Vibrant-Media-Lab/OdysseyNowDaughterCards/OdysseyDaughterCardSpotGenerator/pdf/OdysseyDaughterCardSpotGenerator-B_Cu.pdf

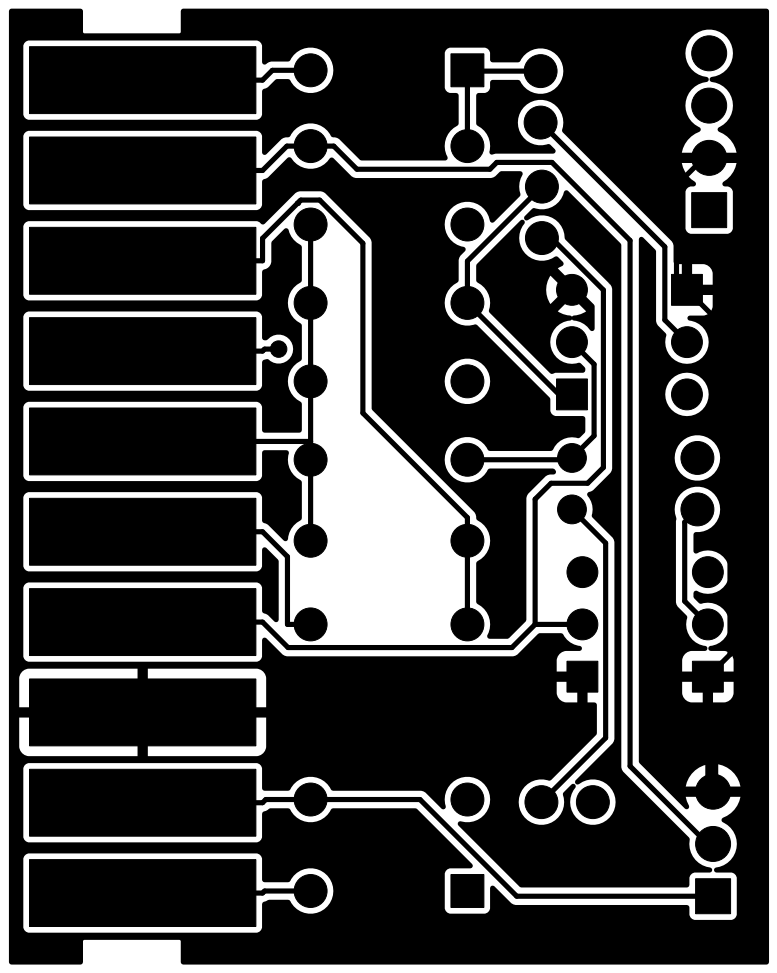
[picture p24: page 1]
