Vibrant-Media-Lab/OdysseyNowDaughterCards/OdysseyDaughterCardSpotGenerator/pdf/OdysseyDaughterCardSpotGenerator-Edge_Cuts.pdf

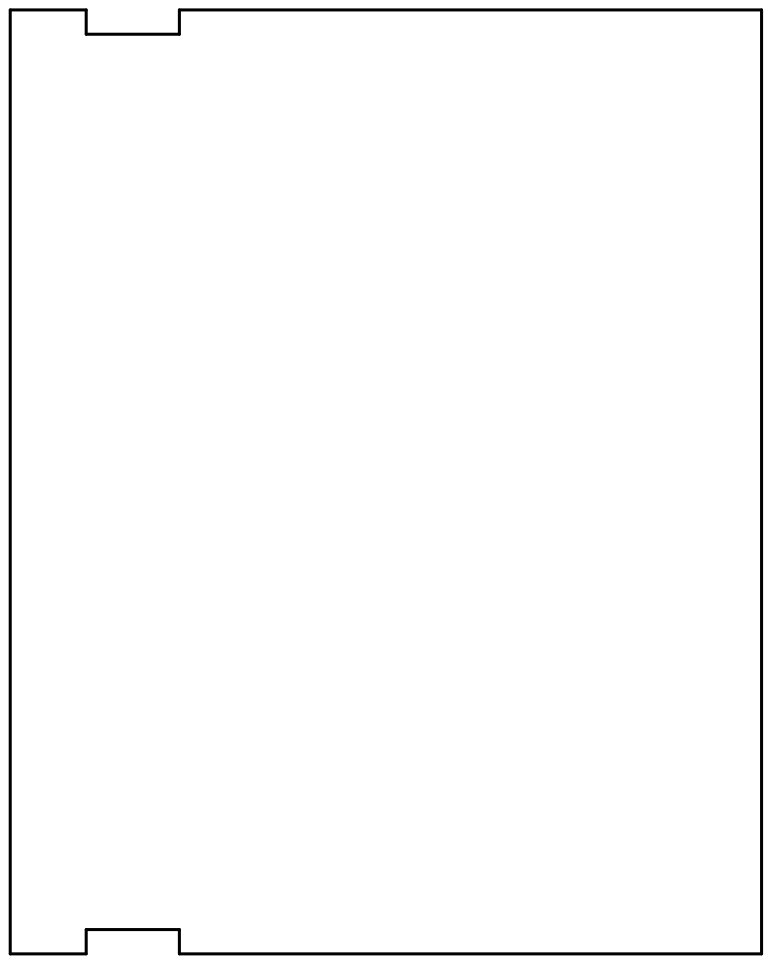
[picture p25: page 1]
