Vibrant-Media-Lab/OdysseyNowDaughterCards/OdysseyDaughterCardSpotGenerator/pdf/OdysseyDaughterCardSpotGenerator-F_Cu.pdf

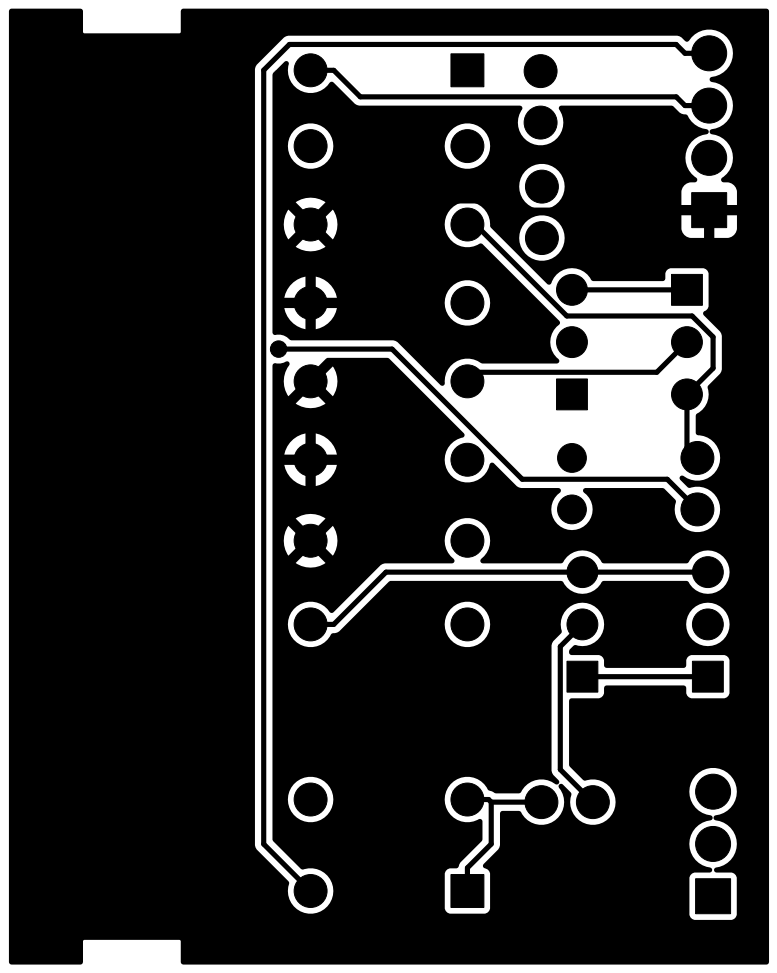
[picture p26: page 1]
