Vibrant-Media-Lab/OdysseyNowDaughterCards/OdysseyDaughterCardSpotGenerator/pdf/OdysseyDaughterCardSpotGenerator-F_Silkscreen.pdf

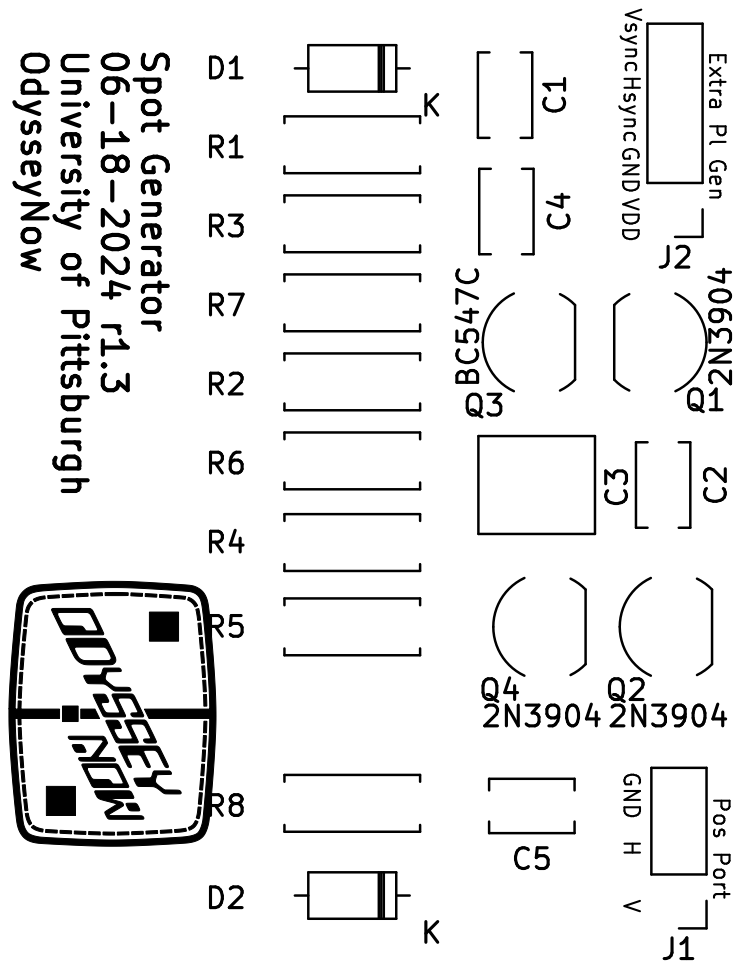
[picture p27: page 1]
