Vibrant-Media-Lab/OdysseyNowDaughterCards/OdysseyDaughterCardSpotGenerator/pdf/OdysseyDaughterCardSpotGenerator.pdf

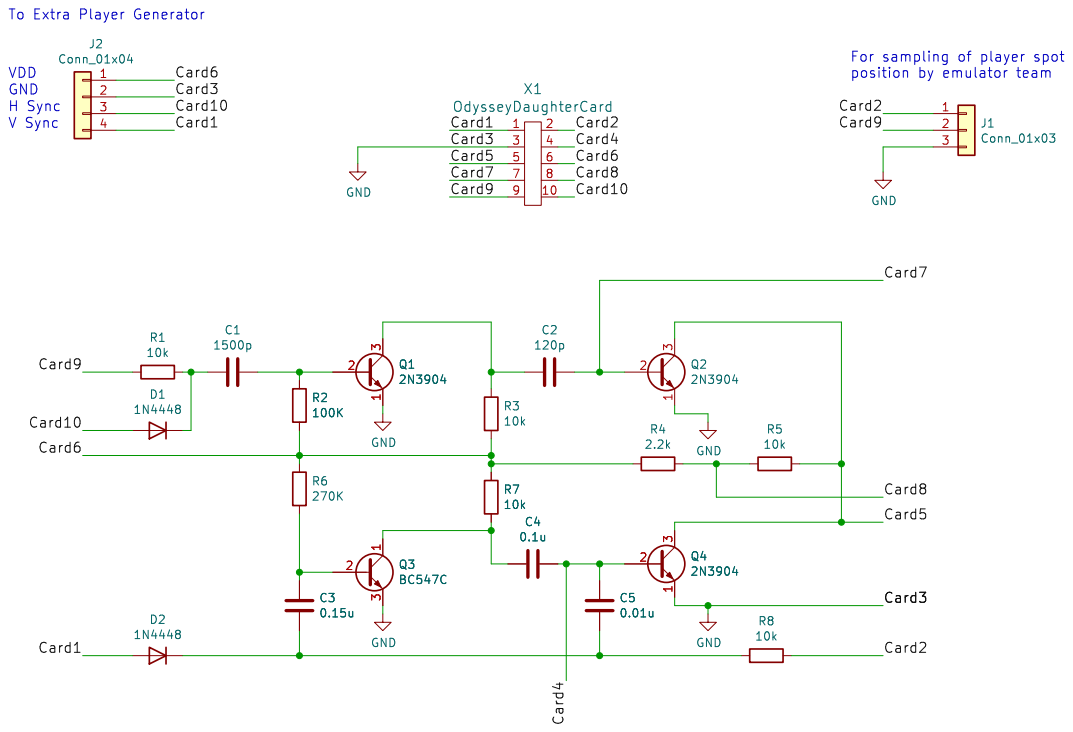
[picture p28: page 1]
