Vibrant-Media-Lab/OdysseyNowDaughterCards/OdysseyDaughterCardHorizSyncGenerator/pdf/OdysseyDaughterCardHorizSyncGenerator-B_Cu.pdf

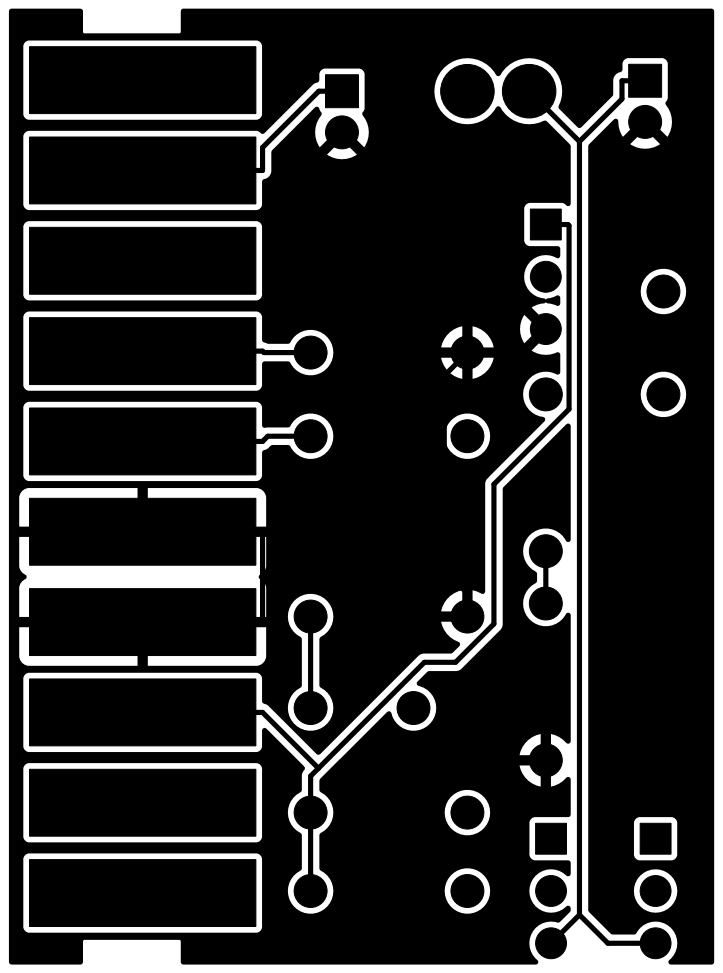
[picture p29: page 1]
