Vibrant-Media-Lab/OdysseyNowDaughterCards/OdysseyDaughterCardHorizSyncGenerator/pdf/OdysseyDaughterCardHorizSyncGenerator-Edge_Cuts.pdf

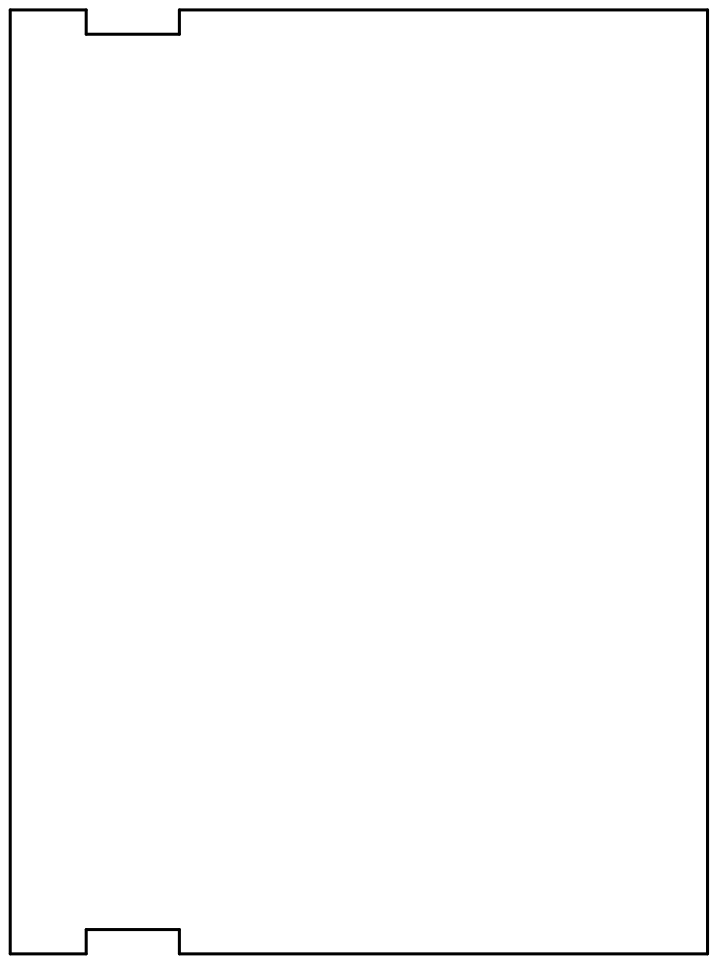
[picture p30: page 1]
