Vibrant-Media-Lab/OdysseyNowDaughterCards/OdysseyDaughterCardHorizSyncGenerator/pdf/OdysseyDaughterCardHorizSyncGenerator-F_Cu.pdf

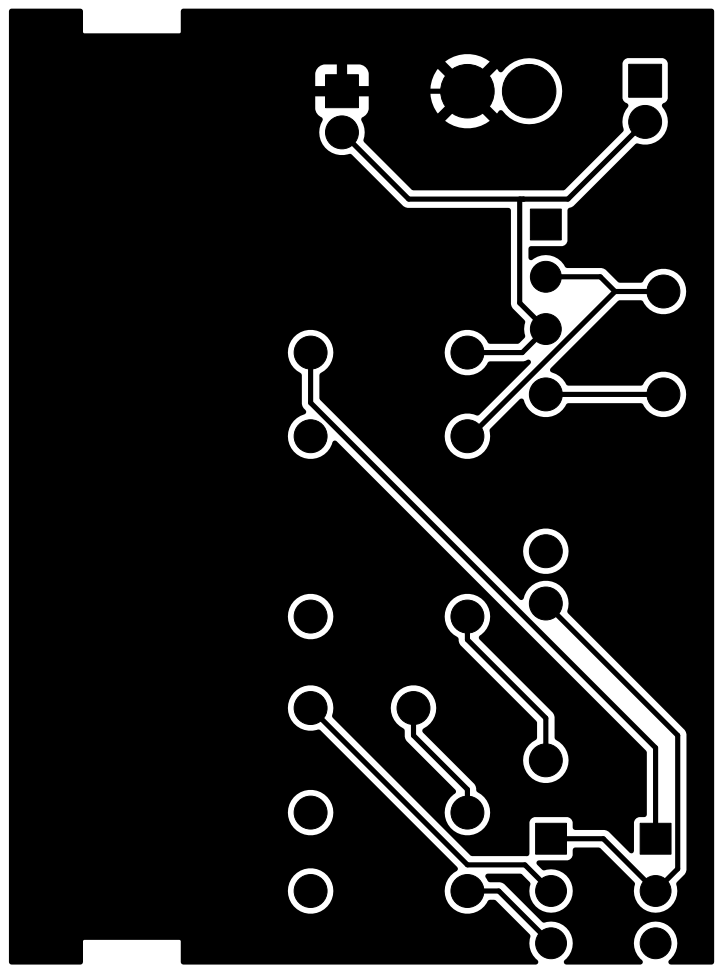
[picture p31: page 1]
