Vibrant-Media-Lab/OdysseyNowDaughterCards/OdysseyDaughterCardHorizSyncGenerator/pdf/OdysseyDaughterCardHorizSyncGenerator-F_Silkscreen.pdf

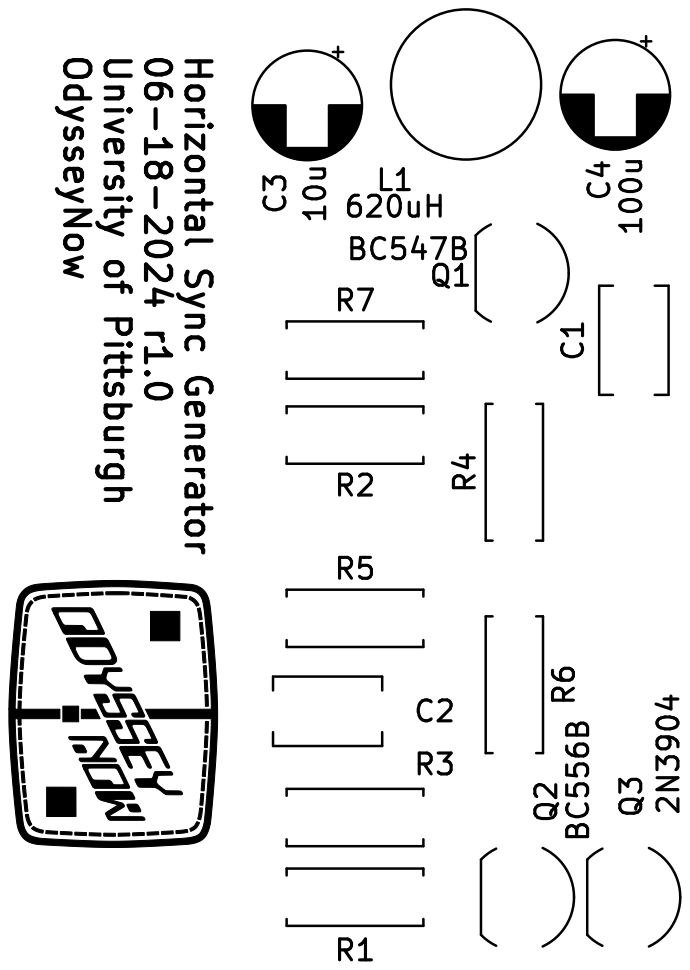
[picture p32: page 1]
