Vibrant-Media-Lab/OdysseyNowDaughterCards/OdysseyDaughterCardHorizSyncGenerator/pdf/OdysseyDaughterCardHorizSyncGenerator.pdf

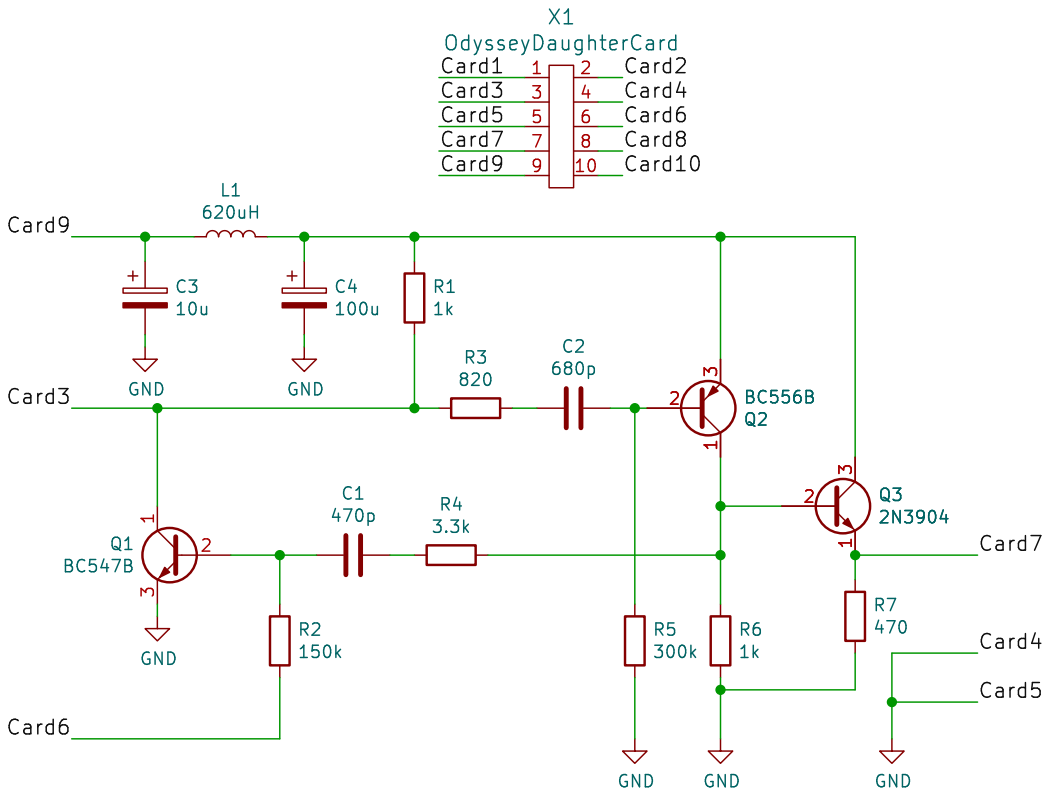
[picture p33: page 1]
