Vibrant-Media-Lab/OdysseyNowDaughterCards/OdysseyDaughterCardGateMatrix/pdf/OdysseyDaughterCardGateMatrix-B_Cu.pdf

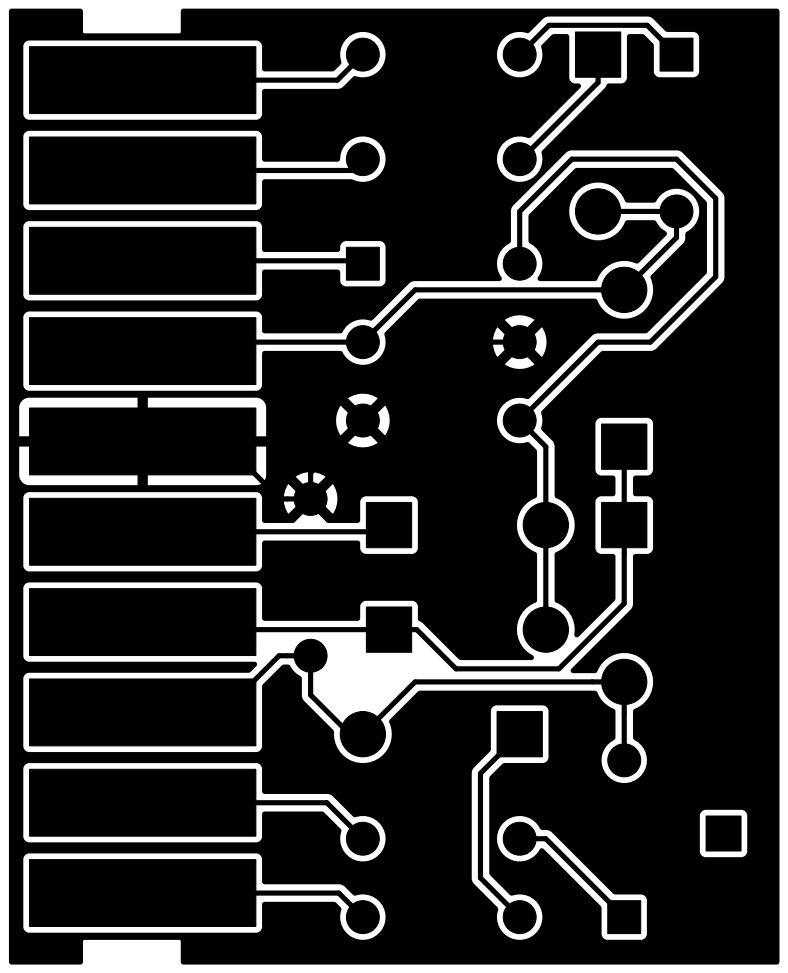
[picture p34: page 1]

Id: 1/1 Title: Odyssey Daughter Card Gate Matrix
