Vibrant-Media-Lab/OdysseyNowDaughterCards/OdysseyDaughterCardGateMatrix/pdf/OdysseyDaughterCardGateMatrix-B_Silkscreen.pdf

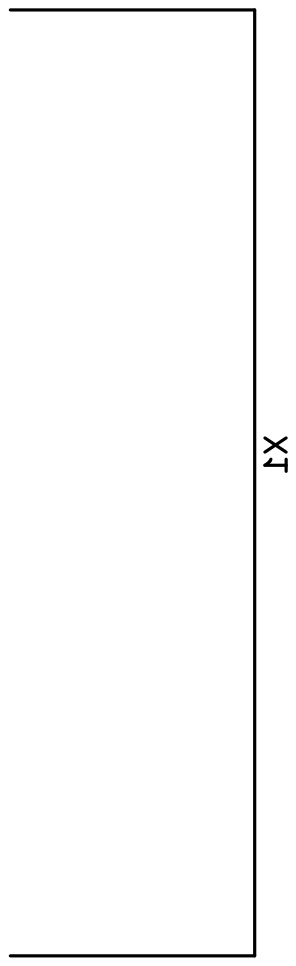
[picture p35: page 1]

Id: 1/1 Title: Odyssey Daughter Card Gate Matrix
