Vibrant-Media-Lab/OdysseyNowDaughterCards/OdysseyDaughterCardGateMatrix/pdf/OdysseyDaughterCardGateMatrix-Edge_Cuts.pdf

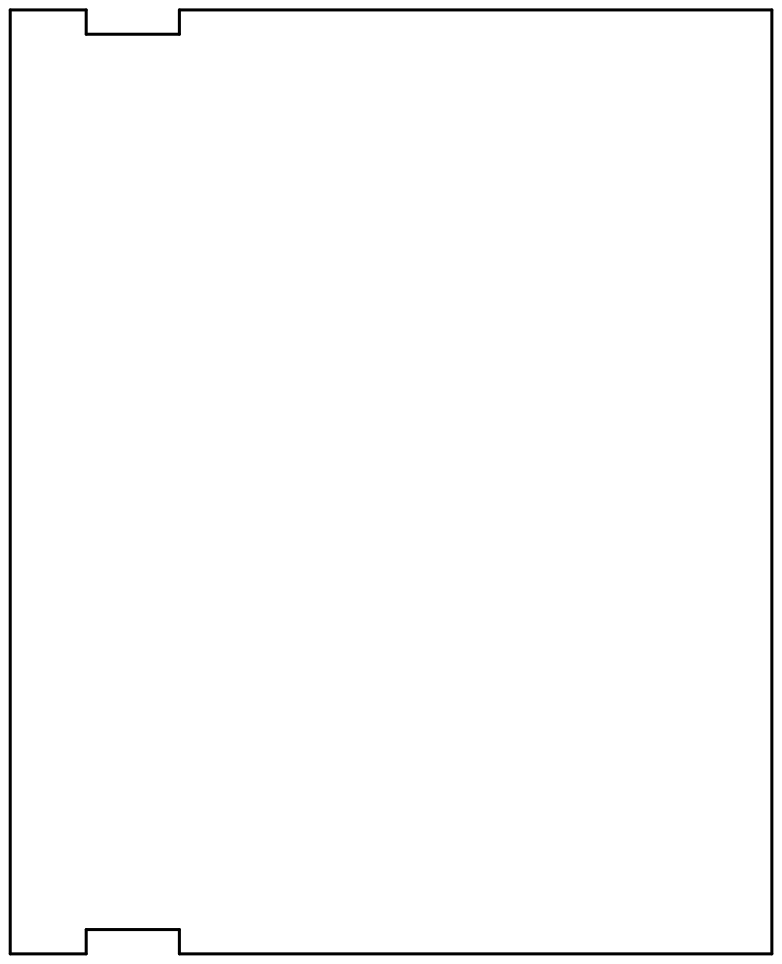
[picture p36: page 1]

Id: 1/1 Title: Odyssey Daughter Card Gate Matrix
