Vibrant-Media-Lab/OdysseyNowDaughterCards/OdysseyDaughterCardGateMatrix/pdf/OdysseyDaughterCardGateMatrix-F_Cu.pdf

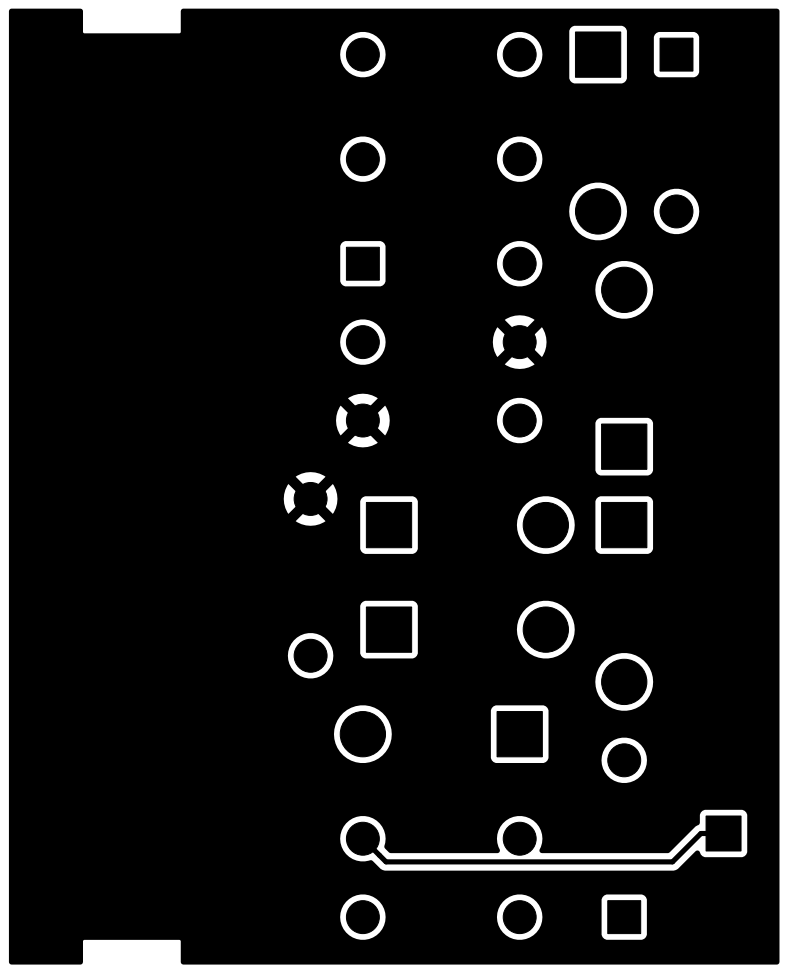
[picture p37: page 1]

Id: 1/1 Title: Odyssey Daughter Card Gate Matrix
