Vibrant-Media-Lab/OdysseyNowDaughterCards/OdysseyDaughterCardGateMatrix/pdf/OdysseyDaughterCardGateMatrix-F_Silkscreen.pdf

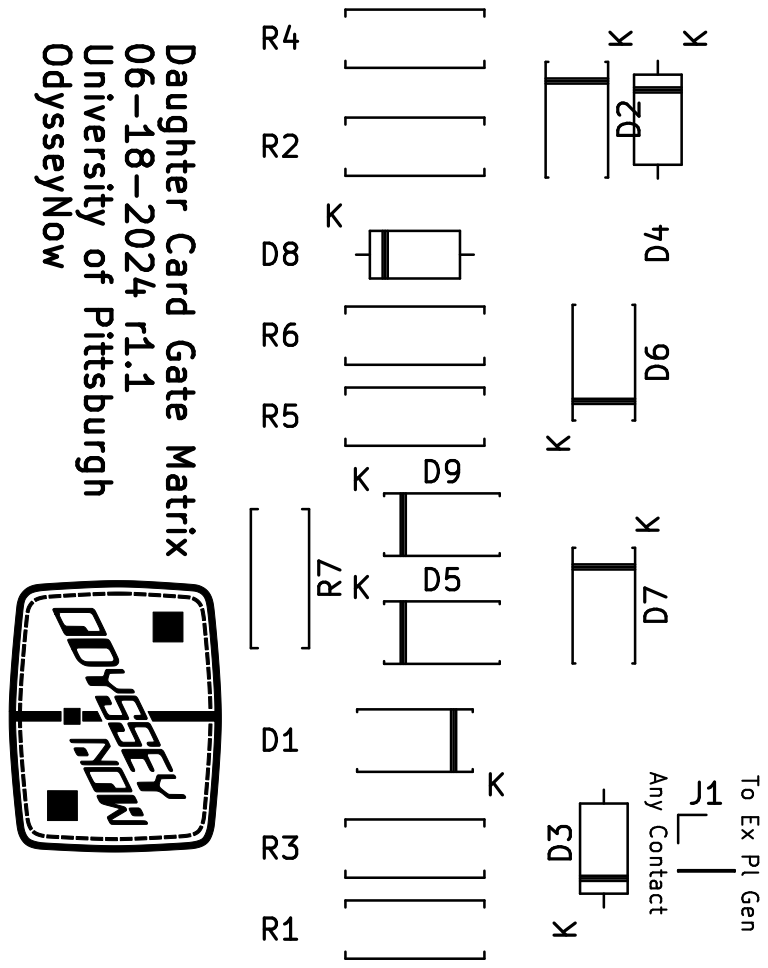
[picture p38: page 1]

Id: 1/1 Title: Odyssey Daughter Card Gate Matrix
