Vibrant-Media-Lab/OdysseyNowDaughterCards/OdysseyDaughterCardGateMatrix/pdf/OdysseyDaughterCardGateMatrix.pdf

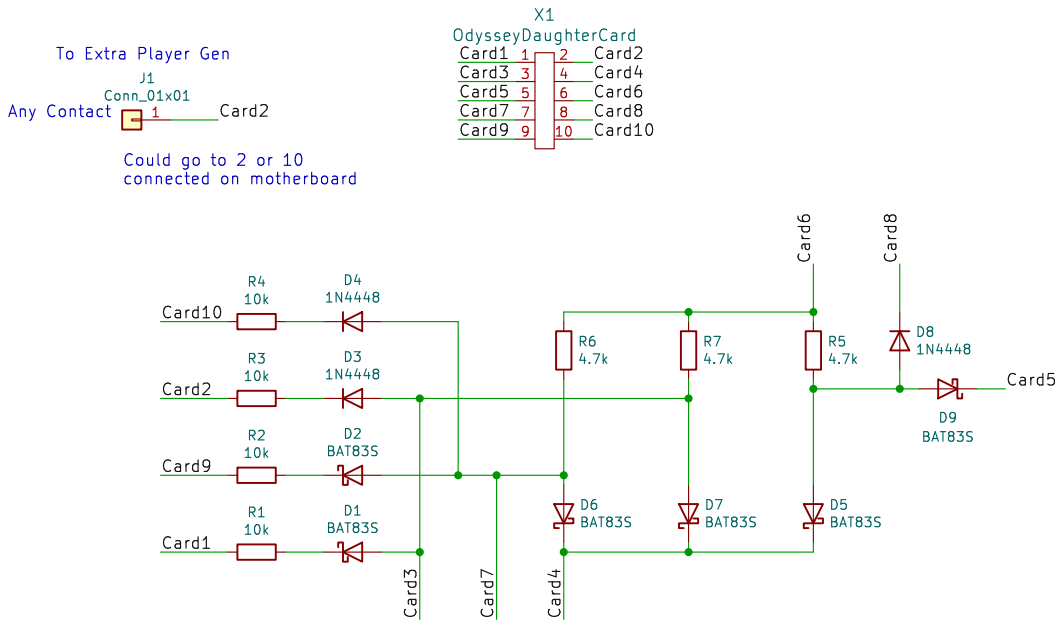
[picture p39: page 1]

Id: 1/1 Title: Odyssey Daughter Card Gate Matrix
