Vibrant-Media-Lab/OdysseyNowDaughterCards/OdysseyDaughterCardFlipFlop/pdf/OdysseyDaughterCardFlipFlop-B_Cu.pdf

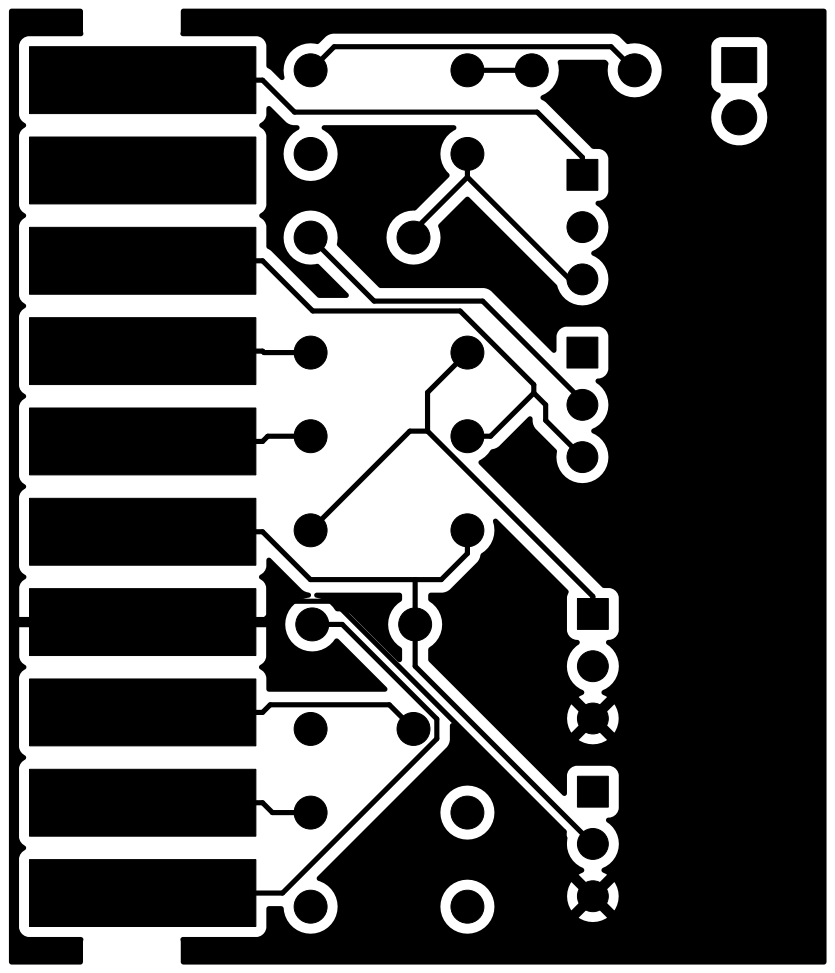
[picture p40: page 1]

Id: 1/1 Title: Odyssey Daughter Card Flip Flop
