Vibrant-Media-Lab/OdysseyNowDaughterCards/OdysseyDaughterCardFlipFlop/pdf/OdysseyDaughterCardFlipFlop-B_Silkscreen.pdf

Id: 1/1 Title: Odyssey Daughter Card Flip Flop
