Vibrant-Media-Lab/OdysseyNowDaughterCards/OdysseyDaughterCardFlipFlop/pdf/OdysseyDaughterCardFlipFlop-Edge_Cuts.pdf

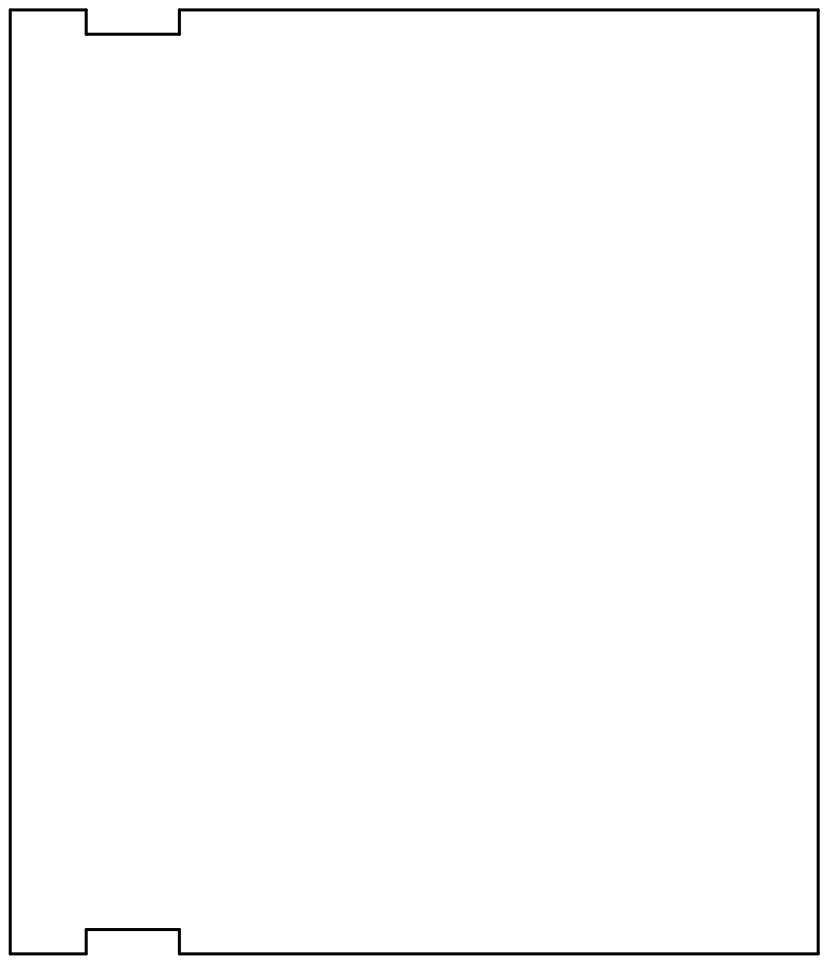
[picture p41: page 1]

Id: 1/1 Title: Odyssey Daughter Card Flip Flop
