Vibrant-Media-Lab/OdysseyNowDaughterCards/OdysseyDaughterCardFlipFlop/pdf/OdysseyDaughterCardFlipFlop-F_Cu.pdf

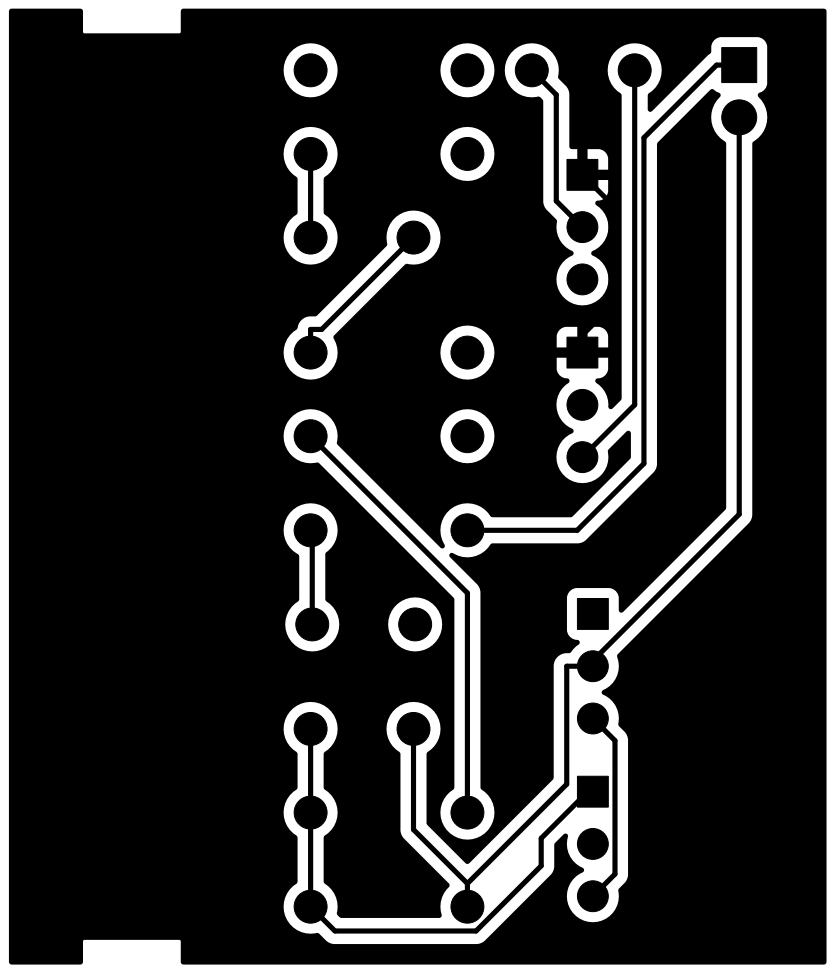
[picture p42: page 1]

Id: 1/1 Title: Odyssey Daughter Card Flip Flop
