Vibrant-Media-Lab/OdysseyNowDaughterCards/OdysseyDaughterCardFlipFlop/pdf/OdysseyDaughterCardFlipFlop-F_Silkscreen.pdf

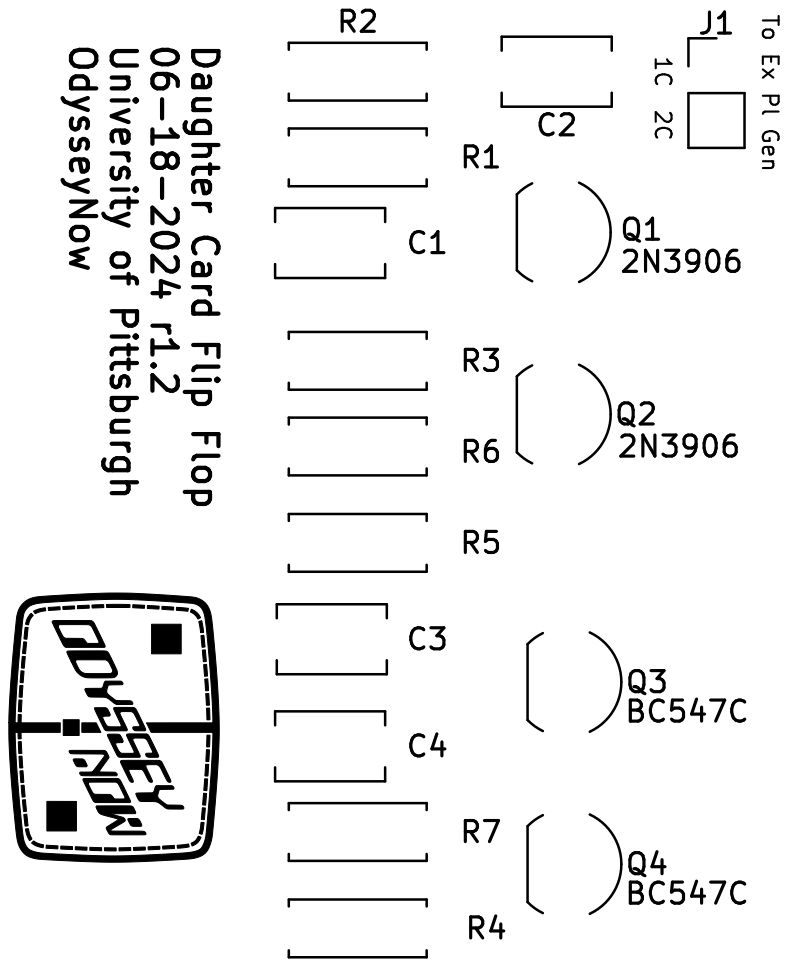
[picture p43: page 1]

Id: 1/1 Title: Odyssey Daughter Card Flip Flop
