Vibrant-Media-Lab/OdysseyNowDaughterCards/OdysseyDaughterCardFlipFlop/pdf/OdysseyDaughterCardFlipFlop.pdf

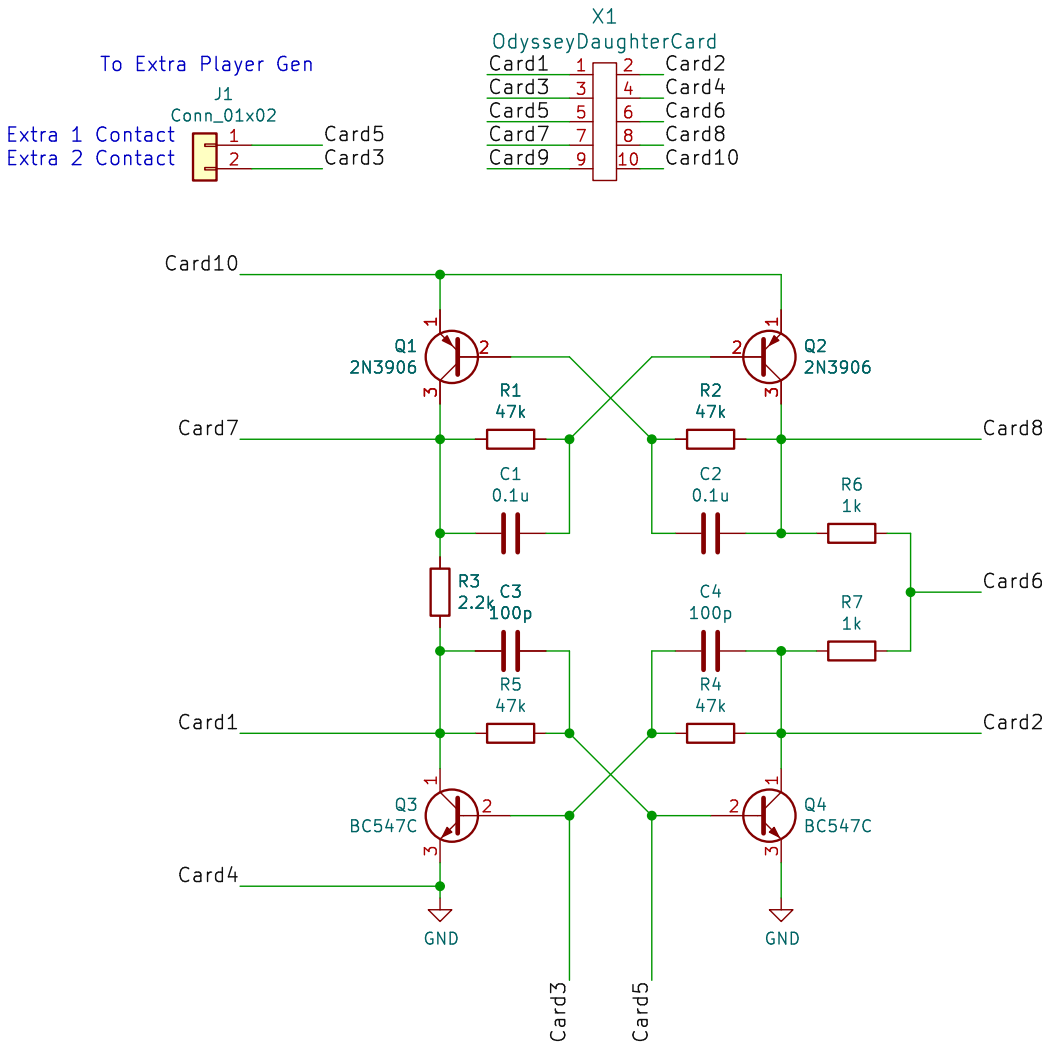
[picture p44: page 1]

Id: 1/1 Title: Odyssey Daughter Card Flip Flop
